crimeofheart/giulietta-blue-me/experiments/standby/data/2026-09-25-halted-split-power.csv

unix_time | volts | amps | watts
1790343489.390 | 5.0844 | 0.1661 | 0.8445
1790343489.660 | 5.0834 | 0.1628 | 0.8276
1790343489.888 | 5.0833 | 0.1514 | 0.7699
1790343490.155 | 5.0835 | 0.1961 | 0.9971
1790343490.381 | 5.0830 | 0.1695 | 0.8617
1790343490.651 | 5.0831 | 0.1517 | 0.7711
1790343490.875 | 5.0833 | 0.1507 | 0.7661
1790343491.190 | 5.0840 | 0.1224 | 0.6223
1790343491.370 | 5.0851 | 0.1221 | 0.6211
1790343491.687 | 5.0858 | 0.1214 | 0.6175
1790343491.865 | 5.0859 | 0.1323 | 0.6732
1790343492.182 | 5.0855 | 0.1211 | 0.6162
1790343492.360 | 5.0856 | 0.1487 | 0.7563
1790343492.675 | 5.0854 | 0.1321 | 0.6718
1790343492.858 | 5.0855 | 0.1321 | 0.6721
1790343493.170 | 5.0851 | 0.1832 | 0.9317
1790343493.350 | 5.0841 | 0.1820 | 0.9253
1790343493.668 | 5.0829 | 0.1849 | 0.9402
1790343493.892 | 5.0938 | 0.1224 | 0.6235
1790343494.160 | 5.0827 | 0.1325 | 0.6739
1790343494.387 | 5.0938 | 0.1263 | 0.6437
1790343494.655 | 5.0850 | 0.1431 | 0.7277
1790343494.882 | 5.0854 | 0.1529 | 0.7778
1790343495.150 | 5.0848 | 0.1438 | 0.7315
1790343495.375 | 5.0844 | 0.1494 | 0.7600
1790343495.691 | 5.0839 | 0.1577 | 0.8017
1790343495.872 | 5.0840 | 0.1790 | 0.9101
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
