crimeofheart/giulietta-blue-me/experiments/standby/data/2026-09-25-power.csv

unix_time | volts | amps | watts
1790337396.228 | 5.0659 | 0.1735 | 0.8792
1790337396.543 | 5.0669 | 0.2212 | 1.1209
1790337396.769 | 5.0680 | 0.1723 | 0.8733
1790337397.038 | 5.0698 | 0.1757 | 0.8911
1790337397.263 | 5.0703 | 0.1725 | 0.8746
1790337397.533 | 5.0714 | 0.1248 | 0.6333
1790337397.758 | 5.0600 | 0.2224 | 1.1257
1790337398.029 | 5.0719 | 0.1464 | 0.7429
1790337398.253 | 5.0720 | 0.1430 | 0.7254
1790337398.568 | 5.0722 | 0.1599 | 0.8111
1790337398.748 | 5.0722 | 0.1596 | 0.8097
1790337399.064 | 5.0739 | 0.1464 | 0.7430
1790337399.243 | 5.0743 | 0.1668 | 0.8466
1790337399.559 | 5.0745 | 0.1424 | 0.7227
1790337399.738 | 5.0743 | 0.1438 | 0.7297
1790337400.053 | 5.0743 | 0.1802 | 0.9147
1790337400.233 | 5.0735 | 0.1656 | 0.8402
1790337400.548 | 5.0725 | 0.1837 | 0.9320
1790337400.729 | 5.0718 | 0.1578 | 0.8006
1790337401.043 | 5.0700 | 0.2229 | 1.1304
1790337401.268 | 5.0699 | 0.1906 | 0.9667
1790337401.538 | 5.0588 | 0.2224 | 1.1254
1790337401.763 | 5.0693 | 0.1541 | 0.7816
1790337402.034 | 5.0703 | 0.1859 | 0.9429
1790337402.259 | 5.0705 | 0.1536 | 0.7792
1790337402.528 | 5.0710 | 0.1857 | 0.9418
1790337402.753 | 5.0713 | 0.1635 | 0.8292
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
